Windfisch/analog-synth/measure_vco/experiments/20190922/blue_5.0.png

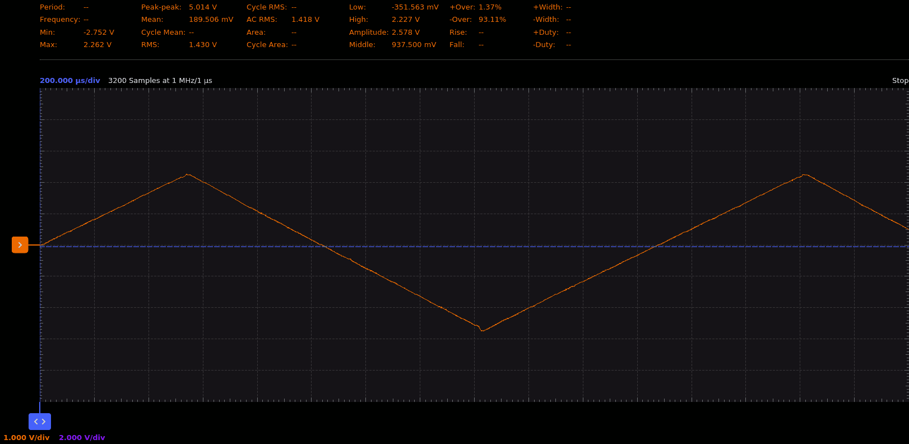
measure_vco/experiments/20190922/blue_5.0.png
