Windfisch/analog-synth/measure_vco/experiments/20190922/breadboard1_8.0.png

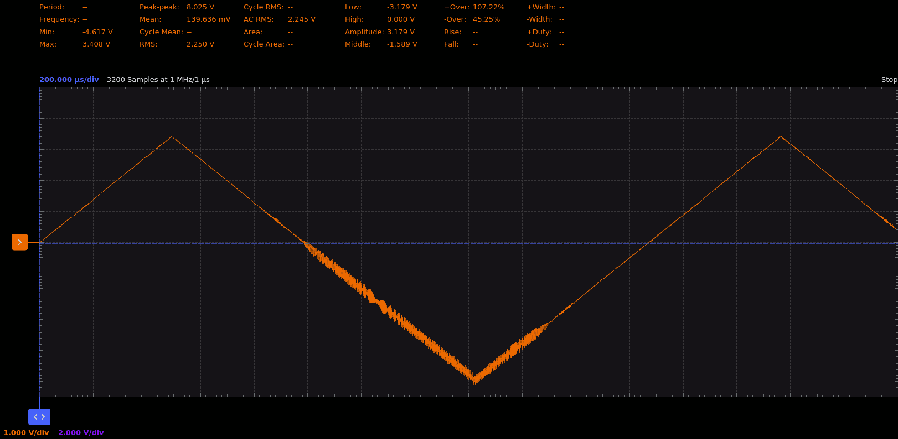
measure_vco/experiments/20190922/breadboard1_8.0.png
