Windfisch/analog-synth/measure_vco/experiments/20190922/breadboard3_2.5.png

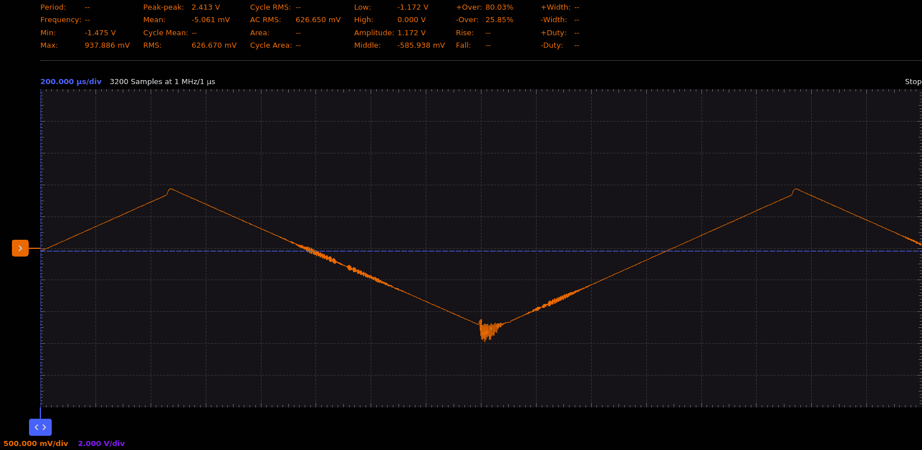
measure_vco/experiments/20190922/breadboard3_2.5.png
