Windfisch/analog-synth/measure_vco/experiments/20190922/breadboard4_2.5.png

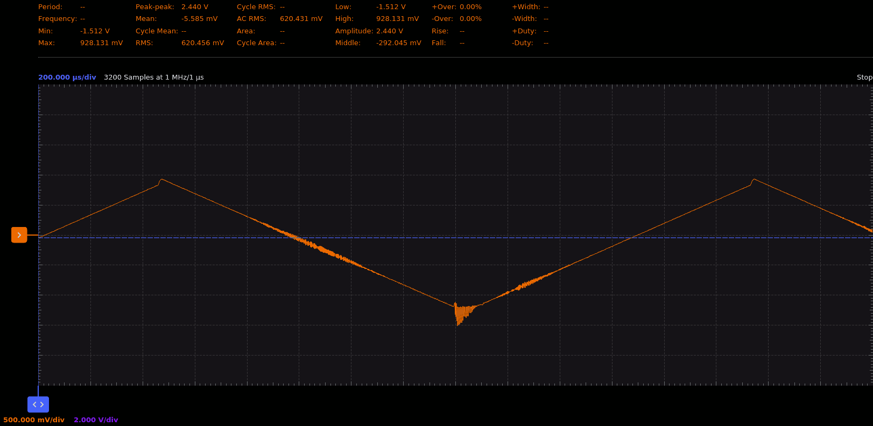
measure_vco/experiments/20190922/breadboard4_2.5.png
