Windfisch/analog-synth/simulation/vca2/vca.kicad_pcb

## KiCad design kicad/HybridIc1.kicad_sch

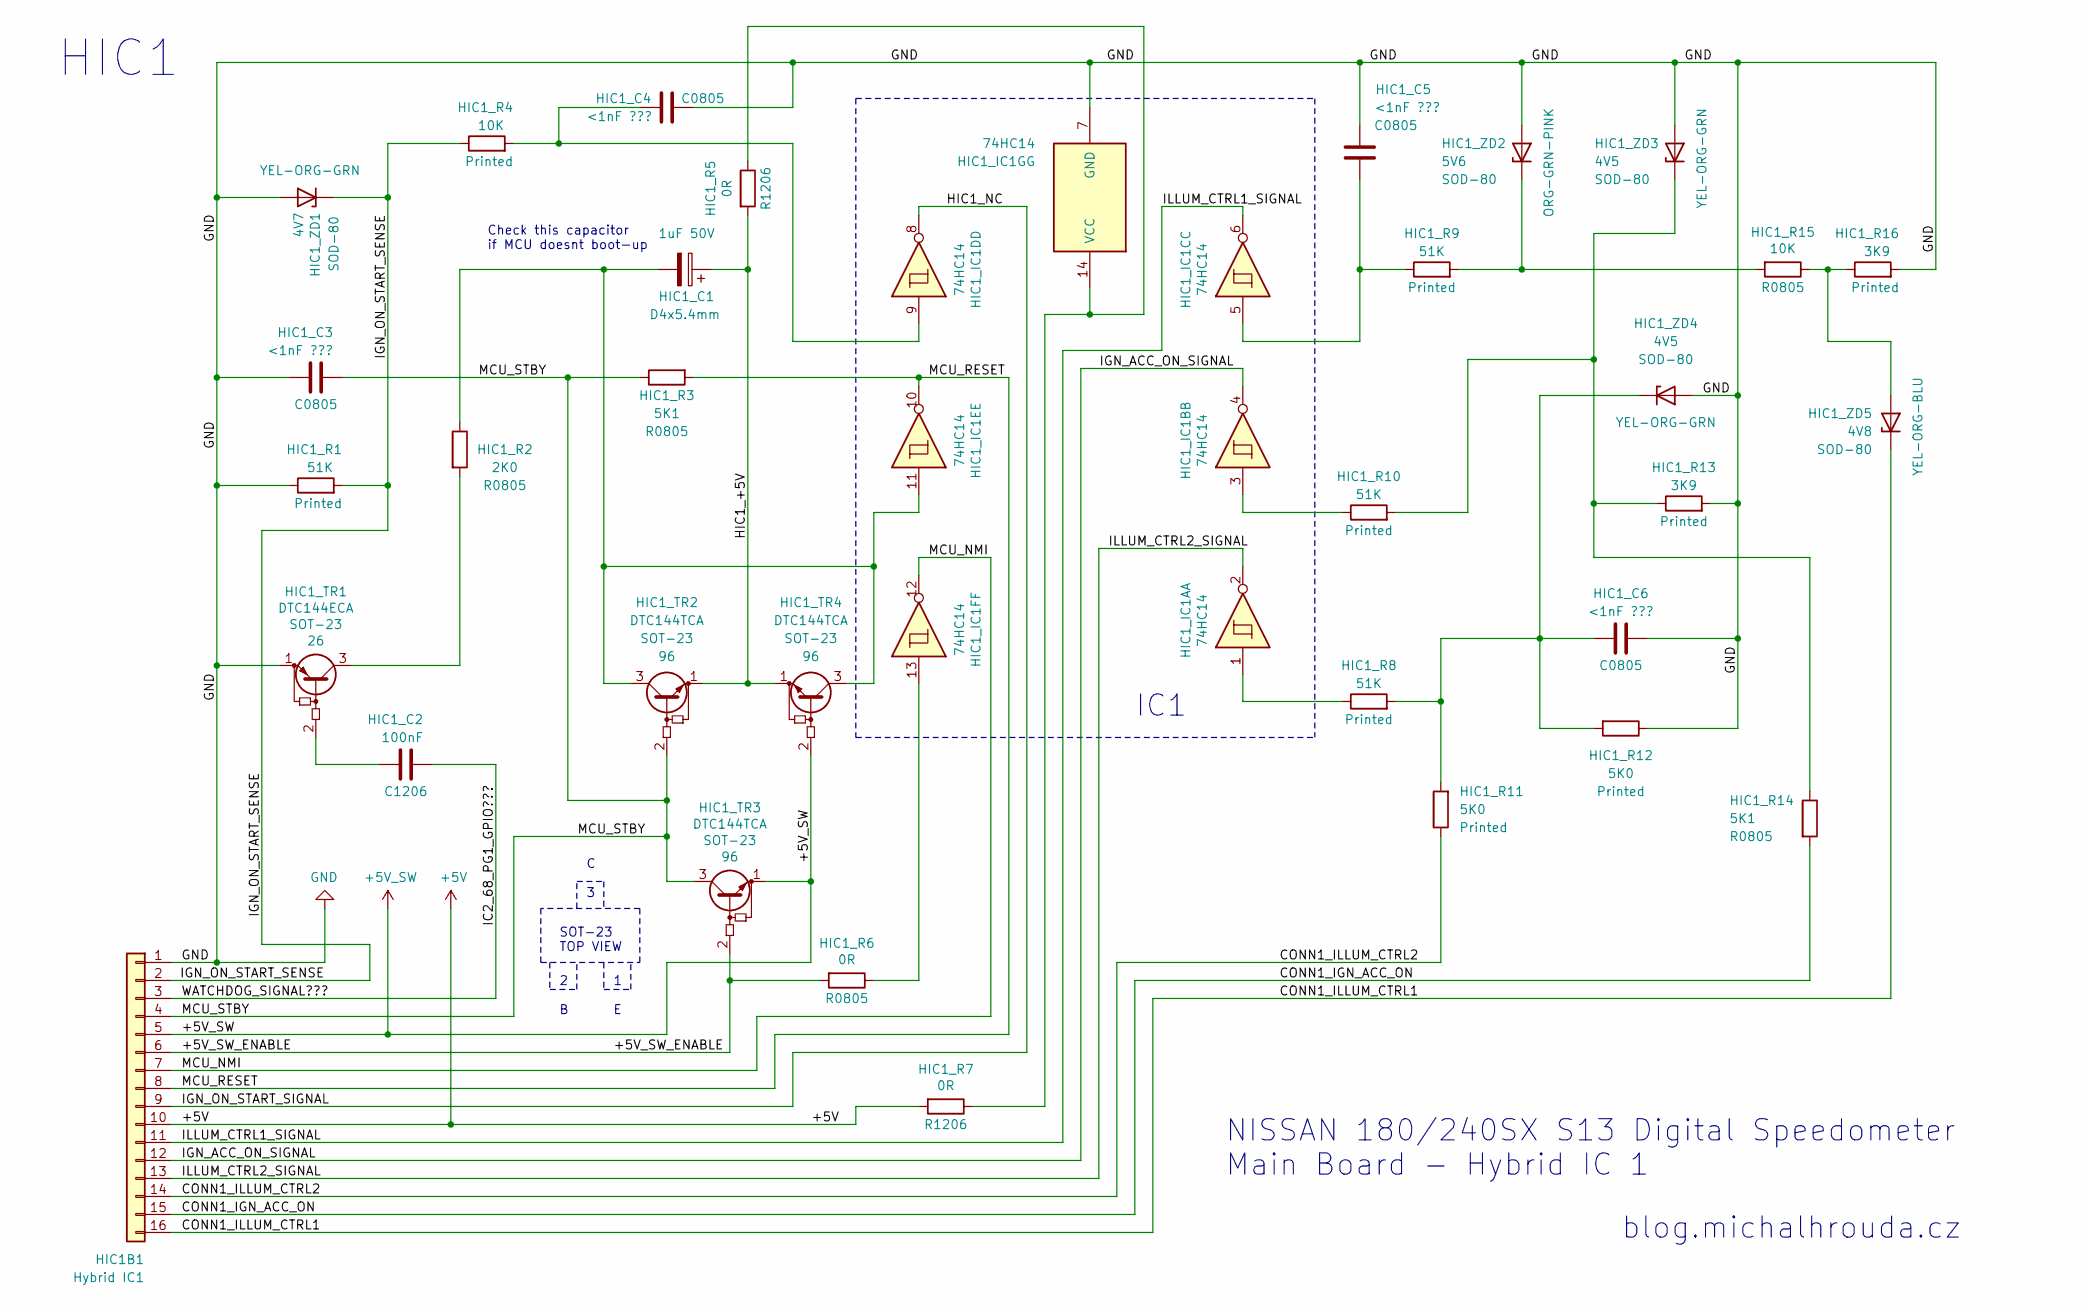
[picture p21: schematic HybridIc1.kicad_sch]

Parts:
HIC1B1: Hybrid IC1
HIC1_C1: 1uF 50V
HIC1_C2: 100nF
HIC1_C3, HIC1_C4, HIC1_C5, HIC1_C6: <1nF ???
HIC1_IC1A, HIC1_IC1B, HIC1_IC1C, HIC1_IC1D, HIC1_IC1E, HIC1_IC1F, HIC1_IC1G: 74HC14
HIC1_R1, HIC1_R8, HIC1_R9, HIC1_R10: 51K
HIC1_R2: 2K0
HIC1_R3, HIC1_R14: 5K1
HIC1_R4, HIC1_R15: 10K
HIC1_R5, HIC1_R6, HIC1_R7: 0R
HIC1_R11, HIC1_R12: 5K0
HIC1_R13, HIC1_R16: 3K9
HIC1_TR1: DTC144ECA
HIC1_TR2, HIC1_TR3, HIC1_TR4: DTC144TCA
HIC1_ZD1: 4V7
HIC1_ZD2: 5V6
HIC1_ZD3, HIC1_ZD4: 4V5
HIC1_ZD5: 4V8

Connections:
+5V: HIC1B1.10, HIC1_R7.2
+5V_SW: HIC1B1.5, HIC1_TR3.1 (E), HIC1_TR4.2 (B)
+5V_SW_ENABLE: HIC1B1.6, HIC1_R6.2, HIC1_TR3.2 (B)
CONN1_IGN_ACC_ON: HIC1B1.15, HIC1_R14.2
CONN1_ILLUM_CTRL1: HIC1B1.16, HIC1_ZD5.1 (K)
CONN1_ILLUM_CTRL2: HIC1B1.14, HIC1_R11.1
GND: HIC1B1.1, HIC1_C3.2, HIC1_C4.2, HIC1_C5.1, HIC1_C6.1, HIC1_IC1G.7 (GND), HIC1_R1.1, HIC1_R12.1, HIC1_R13.2, HIC1_R16.2, HIC1_TR1.1 (E), HIC1_ZD1.2 (A), HIC1_ZD2.2 (A), HIC1_ZD3.2 (A), HIC1_ZD4.2 (A)
HIC1_+5V: HIC1_C1.1, HIC1_R5.2, HIC1_TR2.1 (E), HIC1_TR4.1 (E)
HIC1_NC: HIC1B1.9, HIC1_IC1D.8
IC2_68_PG1_GPIO???: HIC1B1.3, HIC1_C2.1
IGN_ACC_ON_SIGNAL: HIC1B1.12, HIC1_IC1B.4
IGN_ON_START_SENSE: HIC1B1.2, HIC1_R1.2, HIC1_R4.1, HIC1_ZD1.1 (K)
ILLUM_CTRL1_SIGNAL: HIC1B1.11, HIC1_IC1C.6
ILLUM_CTRL2_SIGNAL: HIC1B1.13, HIC1_IC1A.2
MCU_NMI: HIC1B1.7, HIC1_IC1F.12
MCU_RESET: HIC1B1.8, HIC1_IC1E.10, HIC1_R3.2
MCU_STBY: HIC1B1.4, HIC1_C3.1, HIC1_R3.1, HIC1_TR2.2 (B), HIC1_TR3.3 (C)
unnamed: HIC1_C1.2, HIC1_IC1E.11, HIC1_R2.1, HIC1_TR2.3 (C), HIC1_TR4.3 (C)
unnamed: HIC1_C2.2, HIC1_TR1.2 (B)
unnamed: HIC1_C4.1, HIC1_IC1D.9, HIC1_R4.2
unnamed: HIC1_C5.2, HIC1_IC1C.5, HIC1_R9.1
unnamed: HIC1_C6.2, HIC1_R8.2, HIC1_R11.2, HIC1_R12.2, HIC1_ZD4.1 (K)
unnamed: HIC1_IC1A.1, HIC1_R8.1
unnamed: HIC1_IC1B.3, HIC1_R10.1
unnamed: HIC1_IC1F.13, HIC1_R6.1
unnamed: HIC1_IC1G.14 (VCC), HIC1_R5.1, HIC1_R7.1
unnamed: HIC1_R2.2, HIC1_TR1.3 (C)
unnamed: HIC1_R10.2, HIC1_R13.1, HIC1_R14.1, HIC1_ZD3.1 (K)
unnamed: HIC1_R15.1, HIC1_R16.1, HIC1_ZD5.2 (A)
unnamed: HIC1_R9.2, HIC1_R15.2, HIC1_ZD2.1 (K)

Notes on the sheet:
HIC1
NISSAN 180/240SX S13 Digital Speedometer Main Board - Hybrid IC 1
2 B
SOT-23 TOP VIEW
C 3
Check this capacitor if MCU doesnt boot-up
1 E
IC1
blog.michalhrouda.cz
