Windfisch/analog-synth/simulation/vca2/vca.kicad_pcb

## KiCad design kicad/HybridIc3.kicad_sch

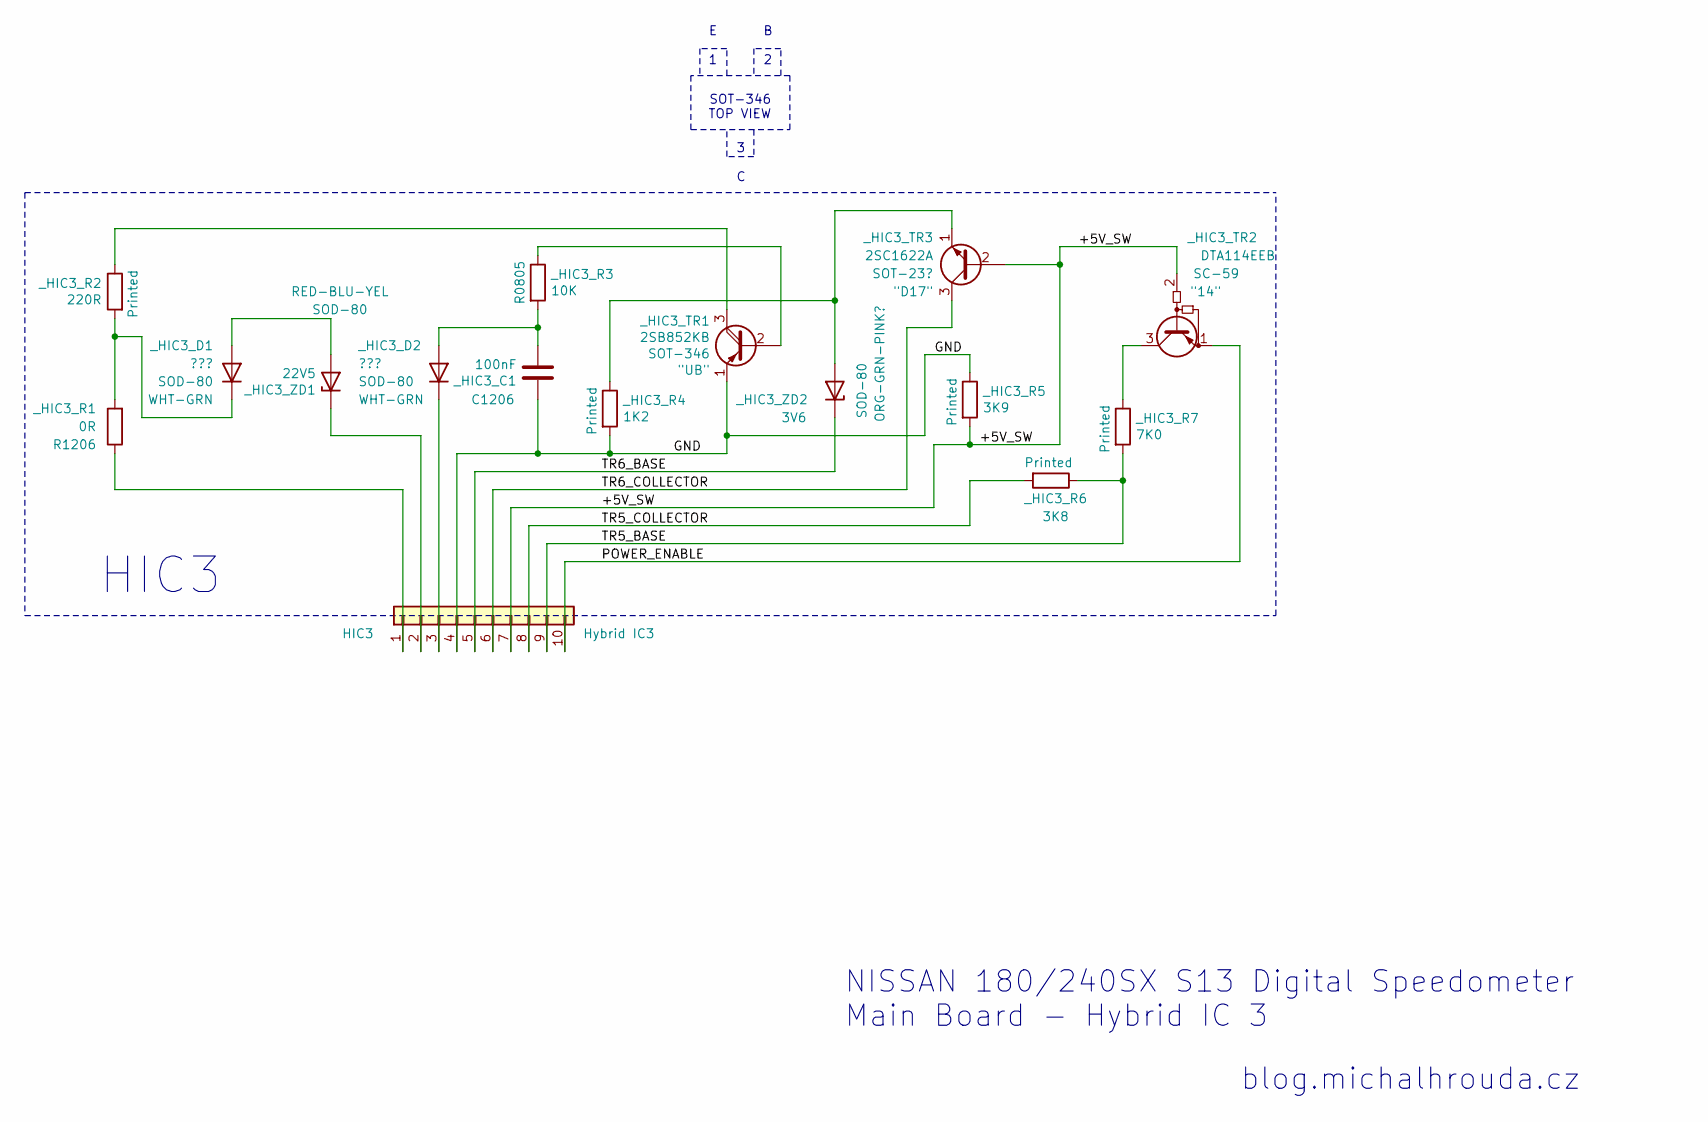
[picture p23: schematic HybridIc3.kicad_sch]

Parts:
HIC3: Hybrid IC3
_HIC3_C1: 100nF
_HIC3_D1, _HIC3_D2: ???
_HIC3_R1: 0R
_HIC3_R2: 220R
_HIC3_R3: 10K
_HIC3_R4: 1K2
_HIC3_R5: 3K9
_HIC3_R6: 3K8
_HIC3_R7: 7K0
_HIC3_TR1: 2SB852KB
_HIC3_TR2: DTA114EEB
_HIC3_TR3: 2SC1622A
_HIC3_ZD1: 22V5
_HIC3_ZD2: 3V6

Connections:
+5V_SW: HIC3.7, _HIC3_R5.2, _HIC3_TR2.2 (B), _HIC3_TR3.2 (B)
GND: HIC3.4, _HIC3_C1.1, _HIC3_R4.2, _HIC3_R5.1, _HIC3_TR1.1 (E)
unnamed: HIC3.1, _HIC3_R1.1
unnamed: HIC3.2, _HIC3_ZD1.1 (K)
unnamed: HIC3.3, _HIC3_D2.1 (K)
unnamed: _HIC3_C1.2, _HIC3_D2.2 (A), _HIC3_R3.2
unnamed: _HIC3_D1.1 (K), _HIC3_R1.2, _HIC3_R2.2
unnamed: _HIC3_D1.2 (A), _HIC3_ZD1.2 (A)
unnamed: _HIC3_R2.1, _HIC3_TR1.3 (C)
unnamed: _HIC3_R3.1, _HIC3_TR1.2 (B)
unnamed: _HIC3_R4.1, _HIC3_TR3.1 (E), _HIC3_ZD2.2 (A)
unnamed: _HIC3_R7.1, _HIC3_TR2.3 (C)
POWER_ENABLE: HIC3.10, _HIC3_TR2.1 (E)
TR5_BASE: HIC3.9, _HIC3_R6.1, _HIC3_R7.2
TR5_COLLECTOR: HIC3.8, _HIC3_R6.2
TR6_BASE: HIC3.5, _HIC3_ZD2.1 (K)
TR6_COLLECTOR: HIC3.6, _HIC3_TR3.3 (C)

Notes on the sheet:
3 C
NISSAN 180/240SX S13 Digital Speedometer Main Board - Hybrid IC 3
E 1
blog.michalhrouda.cz
HIC3
SOT-346 TOP VIEW
B 2
