Windfisch/analog-synth/simulation/vca2/vca.kicad_pcb

## KiCad design kicad/MainBoard.kicad_sch

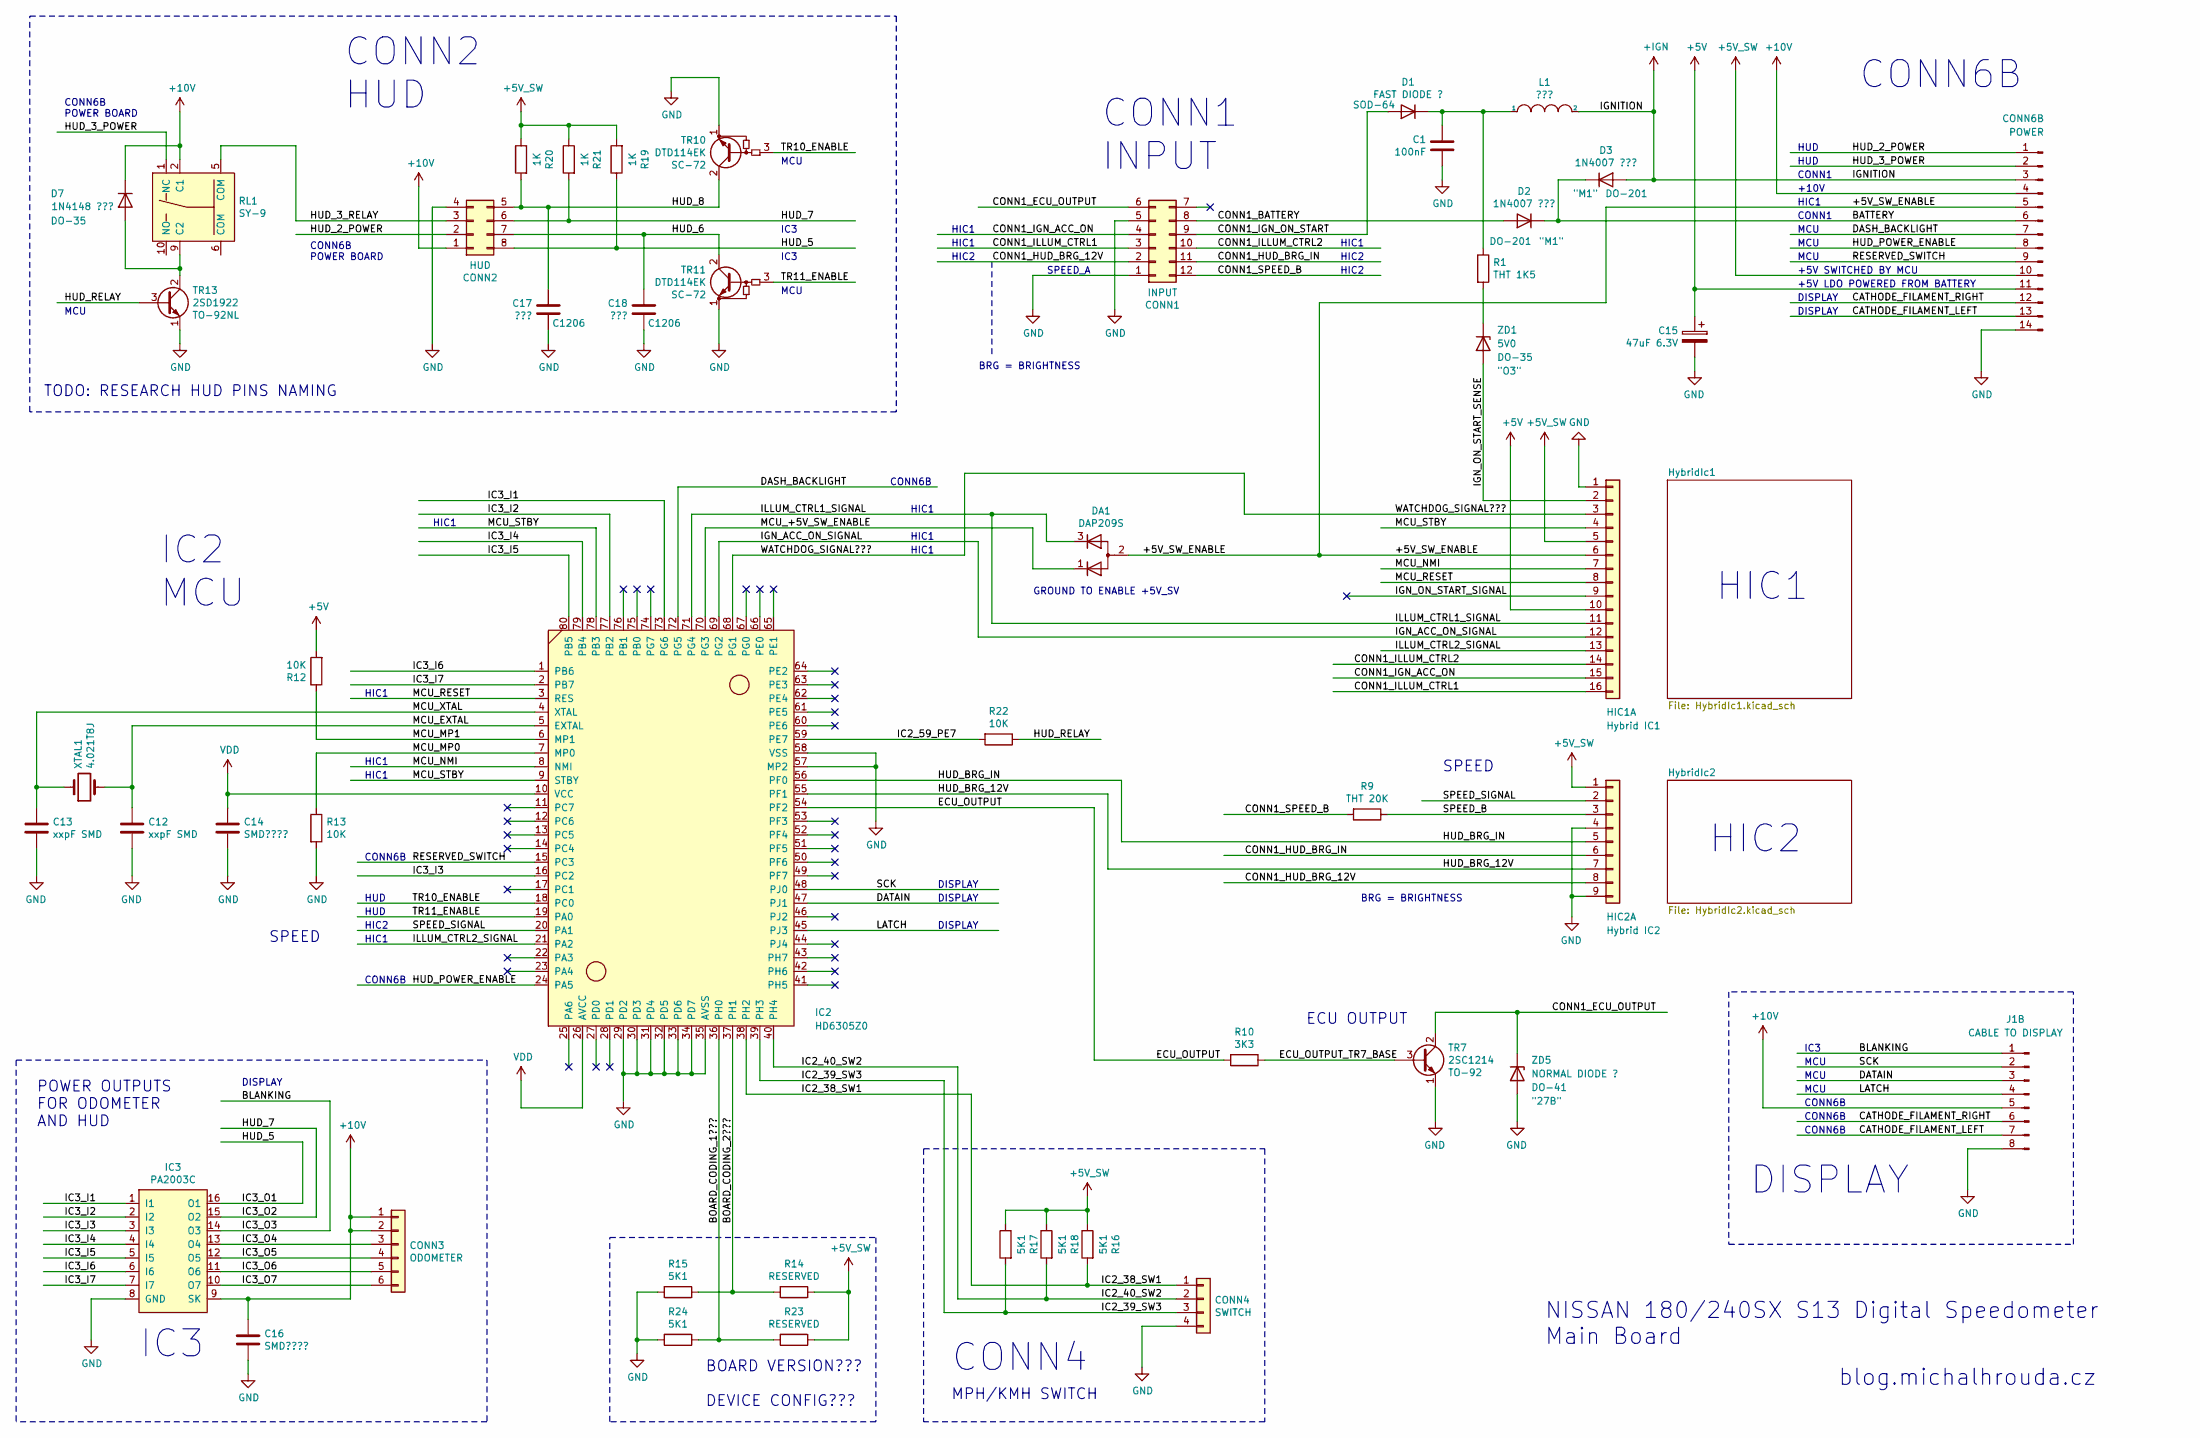
[picture p24: schematic MainBoard.kicad_sch]

Parts:
C1: 100nF
C12, C13: xxpF SMD
C14, C16: SMD????
C15: 47uF 6.3V
C17, C18: ???
CONN1: INPUT
CONN2: HUD
CONN3: ODOMETER
CONN4: SWITCH
CONN6B: POWER
D1: FAST DIODE ?
D2, D3: 1N4007 ???
D7: 1N4148 ???
DA1: DAP209S
HIC1A: Hybrid IC1
HIC2A: Hybrid IC2
IC2: HD6305Z0
IC3: PA2003C
J1B: CABLE TO DISPLAY
L1: ???
R1: THT 1K5
R9: THT 20K
R10: 3K3
R12, R13, R22: 10K
R14, R23: RESERVED
R15, R16, R17, R18, R24: 5K1
R19, R20, R21: 1K
RL1: SY-9
TR7: 2SC1214
TR10, TR11: DTD114EK
TR13: 2SD1922
XTAL1: 4.021T8J
ZD1: 5V0
ZD5: NORMAL DIODE ?

Connections:
+5V: C15.1, CONN6B.11, HIC1A.10, R12.2
+5V_SW: CONN6B.10, HIC1A.5, HIC2A.1, R14.1, R16.1, R17.1, R18.1, R19.2, R20.1, R21.1, R23.1
+5V_SW_ENABLE: CONN6B.5, DA1.2 (A), HIC1A.6
+10V: C16.1, CONN2.1, CONN3.1, CONN3.2, CONN6B.4, D7.1 (K), IC3.9 (SK), J1B.5, RL1.2 (C1)
+IGN: CONN6B.3, D3.2 (A), L1.2
BATTERY: CONN6B.6, D2.1 (K), D3.1 (K)
BLANKING: IC3.14 (O3), J1B.1
BOARD_CODING_1???: IC2.36 (PH0), R23.2, R24.1
BOARD_CODING_2???: IC2.37 (PH1), R14.2, R15.1
CATHODE_FILAMENT_LEFT: CONN6B.13, J1B.7
CATHODE_FILAMENT_RIGHT: CONN6B.12, J1B.6
CONN1_BATTERY: CONN1.8, D2.2 (A)
CONN1_ECU_OUTPUT: CONN1.6, TR7.2 (C), ZD5.1 (K)
CONN1_HUD_BRG_12V: CONN1.2, HIC2A.8
CONN1_HUD_BRG_IN: CONN1.11, HIC2A.6
CONN1_IGN_ACC_ON: CONN1.4, HIC1A.15
CONN1_IGN_ON_START: CONN1.9, D1.2 (A)
CONN1_ILLUM_CTRL1: CONN1.3, HIC1A.16
CONN1_ILLUM_CTRL2: CONN1.10, HIC1A.14
CONN1_SPEED_B: CONN1.12, R9.2
DASH_BACKLIGHT: CONN6B.7, IC2.72 (PG5)
DATAIN: IC2.47 (PJ1), J1B.3
ECU_OUTPUT: IC2.54 (PF2), R10.2
ECU_OUTPUT_TR7_BASE: R10.1, TR7.3 (B)
GND: C1.2, C12.2, C13.2, C14.2, C15.2, C16.2, C17.2, C18.2, CONN1.1, CONN1.5, CONN2.4, CONN4.4, CONN6B.14, HIC1A.1, HIC2A.4, HIC2A.9, IC2.29 (PD2), IC2.30 (PD3), IC2.31 (PD4), IC2.32 (PD5), IC2.33 (PD6), IC2.34 (PD7), IC2.35 (AVSS), IC2.57 (MP2), IC2.58 (VSS), IC3.8 (GND), J1B.8, R13.2, R15.2, R24.2, TR7.1 (E), TR10.1 (E), TR11.1 (E), TR13.1 (E), ZD5.2 (A)
HUD_2_POWER: CONN2.2, CONN6B.1
HUD_3_POWER: CONN6B.2, RL1.1 (NC)
HUD_3_RELAY: CONN2.3, RL1.5 (COM)
HUD_5: CONN2.8, IC3.16 (O1), R19.1
HUD_6: C18.1, CONN2.7, TR11.2 (C)
HUD_7: CONN2.6, IC3.15 (O2), R21.2
HUD_8: C17.1, CONN2.5, R20.2, TR10.2 (C)
HUD_BRG_12V: HIC2A.7, IC2.55 (PF1)
HUD_BRG_IN: HIC2A.5, IC2.56 (PF0)
HUD_POWER_ENABLE: CONN6B.8, IC2.24 (PA5)
HUD_RELAY: R22.1, TR13.3 (B)
IC2_38_SW1: CONN4.1, IC2.38 (PH2), R16.2
IC2_39_SW3: CONN4.3, IC2.39 (PH3), R17.2
IC2_40_SW2: CONN4.2, IC2.40 (PH4), R18.2
IC2_59_PE7: IC2.59 (PE7), R22.2
IC3_I1: IC2.73 (PG6), IC3.1 (I1)
IC3_I2: IC2.77 (PB2), IC3.2 (I2)
IC3_I3: IC2.16 (PC2), IC3.3 (I3)
IC3_I4: IC2.79 (PB4), IC3.4 (I4)
IC3_I5: IC2.80 (PB5), IC3.5 (I5)
IC3_I6: IC2.1 (PB6), IC3.6 (I6)
IC3_I7: IC2.2 (PB7), IC3.7 (I7)
IC3_O4: CONN3.3, IC3.13 (O4)
IC3_O5: CONN3.4, IC3.12 (O5)
IC3_O6: CONN3.5, IC3.11 (O6)
IC3_O7: CONN3.6, IC3.10 (O7)
IGN_ACC_ON_SIGNAL: HIC1A.12, IC2.69 (PG2)
IGN_ON_START_SENSE: HIC1A.2, ZD1.2 (A)
IGN_ON_START_SIGNAL: HIC1A.9
ILLUM_CTRL1_SIGNAL: DA1.3 (K), HIC1A.11, IC2.71 (PG4)
ILLUM_CTRL2_SIGNAL: HIC1A.13, IC2.21 (PA2)
LATCH: IC2.45 (PJ3), J1B.4
MCU_+5V_SW_ENABLE: DA1.1 (K), IC2.70 (PG3)
MCU_EXTAL: C12.1, IC2.5 (EXTAL), XTAL1.2
MCU_MP0: IC2.7 (MP0), R13.1
MCU_MP1: IC2.6 (MP1), R12.1
MCU_NMI: HIC1A.7, IC2.8 (NMI)
MCU_RESET: HIC1A.8, IC2.3 (RES)
MCU_STBY: HIC1A.4, IC2.9 (STBY), IC2.78 (PB3)
MCU_XTAL: C13.1, IC2.4 (XTAL), XTAL1.1
unnamed: C1.1, D1.1 (K), L1.1, R1.1
unnamed: D7.2 (A), RL1.9 (C2), TR13.2 (C)
unnamed: R1.2, ZD1.1 (K)
RESERVED_SWITCH: CONN6B.9, IC2.15 (PC3)
SCK: IC2.48 (PJ0), J1B.2
SPEED_B: HIC2A.3, R9.1
SPEED_SIGNAL: HIC2A.2, IC2.20 (PA1)
TR10_ENABLE: IC2.18 (PC0), TR10.3 (B)
TR11_ENABLE: IC2.19 (PA0), TR11.3 (B)
VDD: C14.1, IC2.10 (VCC), IC2.26 (AVCC)
WATCHDOG_SIGNAL???: HIC1A.3, IC2.68 (PG1)

Notes on the sheet:
MCU
blog.michalhrouda.cz
HIC1
CONN6B
IC3
TODO: RESEARCH HUD PINS NAMING
+10V
BRG = BRIGHTNESS
HIC2
CONN6B POWER BOARD
HUD
BOARD VERSION??? DEVICE CONFIG???
DISPLAY
ECU OUTPUT
+5V SWITCHED BY MCU
SPEED
MPH/KMH SWITCH
NISSAN 180/240SX S13 Digital Speedometer Main Board
CONN4
SPEED_A
CONN1
CONN2 HUD
CONN1 INPUT
+5V LDO POWERED FROM BATTERY
POWER OUTPUTS FOR ODOMETER AND HUD
IC2 MCU
GROUND TO ENABLE +5V_SV
