Windfisch/analog-synth/simulation/vca2/vca.kicad_pcb

## KiCad design kicad/PowerBoard.kicad_sch

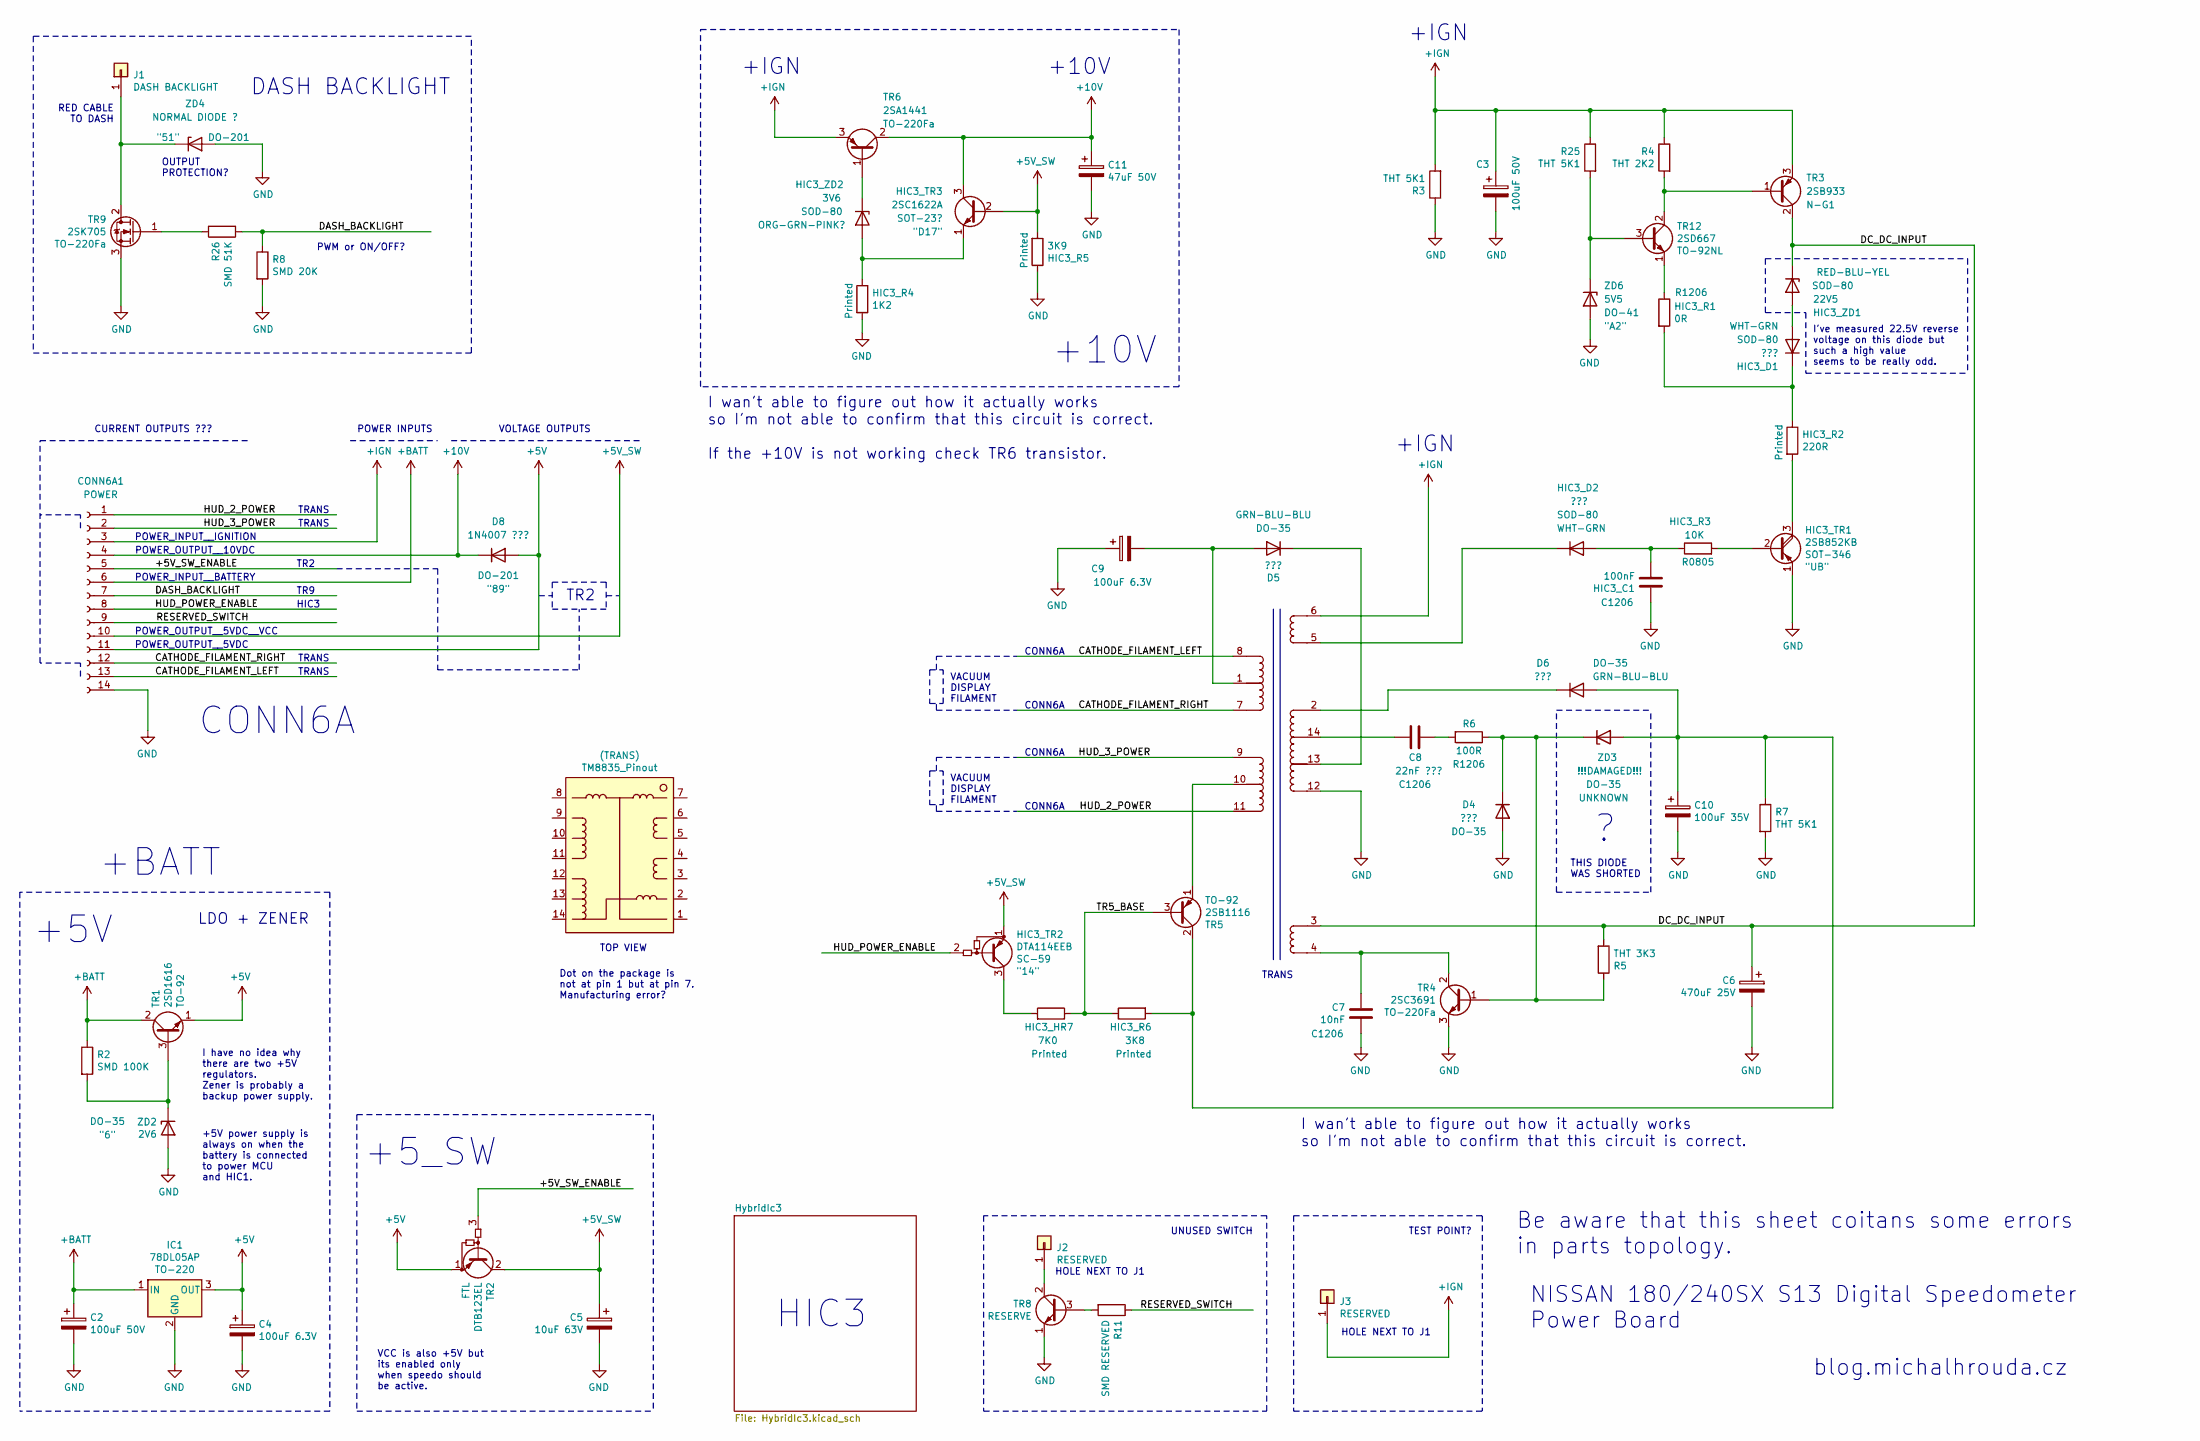
[picture p25: schematic PowerBoard.kicad_sch]

Parts:
(TRANS): TM8835_Pinout
C2, C3: 100uF 50V
C4, C9: 100uF 6.3V
C5: 10uF 63V
C6: 470uF 25V
C7: 10nF
C8: 22nF ???
C10: 100uF 35V
C11: 47uF 50V
CONN6A1: POWER
D4, D5, D6: ???
D8: 1N4007 ???
HIC3_C1: 100nF
HIC3_D1, HIC3_D2: ???
HIC3_HR7: 7K0
HIC3_R1: 0R
HIC3_R2: 220R
HIC3_R3: 10K
HIC3_R4: 1K2
HIC3_R5: 3K9
HIC3_R6: 3K8
HIC3_TR1: 2SB852KB
HIC3_TR2: DTA114EEB
HIC3_TR3: 2SC1622A
HIC3_ZD1: 22V5
HIC3_ZD2: 3V6
IC1: 78DL05AP
J1: DASH BACKLIGHT
J2, J3: RESERVED
R2: SMD 100K
R3, R7, R25: THT 5K1
R4: THT 2K2
R5: THT 3K3
R6: 100R
R8: SMD 20K
R11: SMD RESERVED
R26: SMD 51K
TR1: 2SD1616
TR2: DTB123EL
TR3: 2SB933
TR4: 2SC3691
TR5: 2SB1116
TR6: 2SA1441
TR8: RESERVE
TR9: 2SK705
TR12: 2SD667
TRANS1A, TRANS1B, TRANS1C, TRANS1D, TRANS1E: TM8835
ZD2: 2V6
ZD3: !!!DAMAGED!!!
ZD4: NORMAL DIODE ?
ZD6: 5V5

Connections:
+5V: C4.1, CONN6A1.11, D8.2 (A), IC1.3 (OUT), TR1.1 (E), TR2.1 (E)
+5V_SW: C5.1, CONN6A1.10, HIC3_TR2.1 (E), TR2.2 (C)
+5V_SW_ENABLE: CONN6A1.5, TR2.3 (B)
+10V: C11.1, CONN6A1.4, D8.1 (K), HIC3_TR3.3 (C), TR6.2 (C)
+BATT: C2.1, CONN6A1.6, IC1.1 (IN), R2.1, TR1.2 (C)
+IGN: C3.1, CONN6A1.3, J3.1, R3.2, R4.1, R25.1, TR3.3 (E), TR6.3 (E), TRANS1C.6
CATHODE_FILAMENT_LEFT: CONN6A1.13, TRANS1A.8
CATHODE_FILAMENT_RIGHT: CONN6A1.12, TRANS1A.7
DASH_BACKLIGHT: CONN6A1.7, R8.1, R26.2
DC_DC_INPUT: C6.1, HIC3_ZD1.1 (K), R5.2, TR3.2 (C), TRANS1B.3
GND: C2.2, C3.2, C4.2, C5.2, C6.2, C7.2, C9.1, C10.2, C11.2, CONN6A1.14, D4.2 (A), IC1.2 (GND), R3.1, R7.2, R8.2, TR4.3 (E), TR8.1 (E), TR9.3 (S), TRANS1E.12, ZD2.2 (A), ZD4.2 (A), ZD6.2 (A)
HUD_2_POWER: CONN6A1.1, TRANS1D.11
HUD_3_POWER: CONN6A1.2, TRANS1D.9
HUD_POWER_ENABLE: CONN6A1.8, HIC3_TR2.2 (B)
unnamed: C7.1, TR4.2 (C), TRANS1B.4
unnamed: C8.1, R6.2
unnamed: C8.2, TRANS1E.14
unnamed: C9.2, D5.2 (A), TRANS1A.1
unnamed: C10.1, D6.2 (A), HIC3_R6.2, R7.1, TR5.2 (C), ZD3.2 (A)
unnamed: D4.1 (K), R5.1, R6.1, TR4.1 (B), ZD3.1 (K)
unnamed: D5.1 (K), TRANS1E.13
unnamed: D6.1 (K), TRANS1E.2
unnamed: HIC3_C1.2, HIC3_D2.2 (A), HIC3_R3.1
unnamed: HIC3_D1.1 (K), HIC3_R1.2, HIC3_R2.1
unnamed: HIC3_D1.2 (A), HIC3_ZD1.2 (A)
unnamed: HIC3_D2.1 (K), TRANS1C.5
unnamed: HIC3_HR7.2, HIC3_TR2.3 (C)
unnamed: HIC3_R1.1, TR12.1 (E)
unnamed: HIC3_R2.2, HIC3_TR1.3 (C)
unnamed: HIC3_R3.2, HIC3_TR1.2 (B)
unnamed: HIC3_R4.1, HIC3_TR3.1 (E), HIC3_ZD2.2 (A)
unnamed: HIC3_R5.2, HIC3_TR3.2 (B)
unnamed: HIC3_ZD2.1 (K), TR6.1 (B)
unnamed: J1.1, TR9.2 (D), ZD4.1 (K)
unnamed: J2.1, TR8.2 (C)
unnamed: R2.2, TR1.3 (B), ZD2.1 (K)
unnamed: R4.2, TR3.1 (B), TR12.2 (C)
unnamed: R11.2, TR8.3 (B)
unnamed: R25.2, TR12.3 (B), ZD6.1 (K)
unnamed: R26.1, TR9.1 (G)
unnamed: TR5.1 (E), TRANS1D.10
RESERVED_SWITCH: CONN6A1.9, R11.1
TR5_BASE: HIC3_HR7.1, HIC3_R6.1, TR5.3 (B)

Notes on the sheet:
CONN6A
+10V
I've measured 22.5V reverse voltage on this diode but such a high value seems to be really odd.
Dot on the package is not at pin 1 but at pin 7. Manufacturing error?
VACUUM DISPLAY FILAMENT
+5V
HOLE NEXT TO J1
+5_SW
POWER_OUTPUT__5VDC__VCC
TRANS
UNUSED SWITCH
TEST POINT?
OUTPUT PROTECTION?
POWER INPUTS
I wan't able to figure out how it actually works so I'm not able to confirm that this circuit is correct.
POWER_OUTPUT__5VDC
blog.michalhrouda.cz
I have no idea why there are two +5V regulators. Zener is probably a backup power supply.
+IGN
POWER_INPUT__BATTERY
HIC3
VCC is also +5V but its enabled only when speedo should be active.
TR9
VOLTAGE OUTPUTS
TR2
PWM or ON/OFF?
POWER_INPUT__IGNITION
DASH BACKLIGHT
LDO + ZENER
+BATT
POWER_OUTPUT__10VDC
TOP VIEW
NISSAN 180/240SX S13 Digital Speedometer Power Board
I wan't able to figure out how it actually works so I'm not able to confirm that this circuit is correct. If the +10V is not working check TR6 transistor.
THIS DIODE WAS SHORTED
Be aware that this sheet coitans some errors in parts topology.
RED CABLE TO DASH
+5V power supply is always on when the battery is connected to power MCU and HIC1.
CURRENT OUTPUTS ???
