Windfisch/analog-synth/measure_vco/schem/measure_vco.sch

## KiCad design measure_vco/schem/measure_vco.sch (2019-10-25)

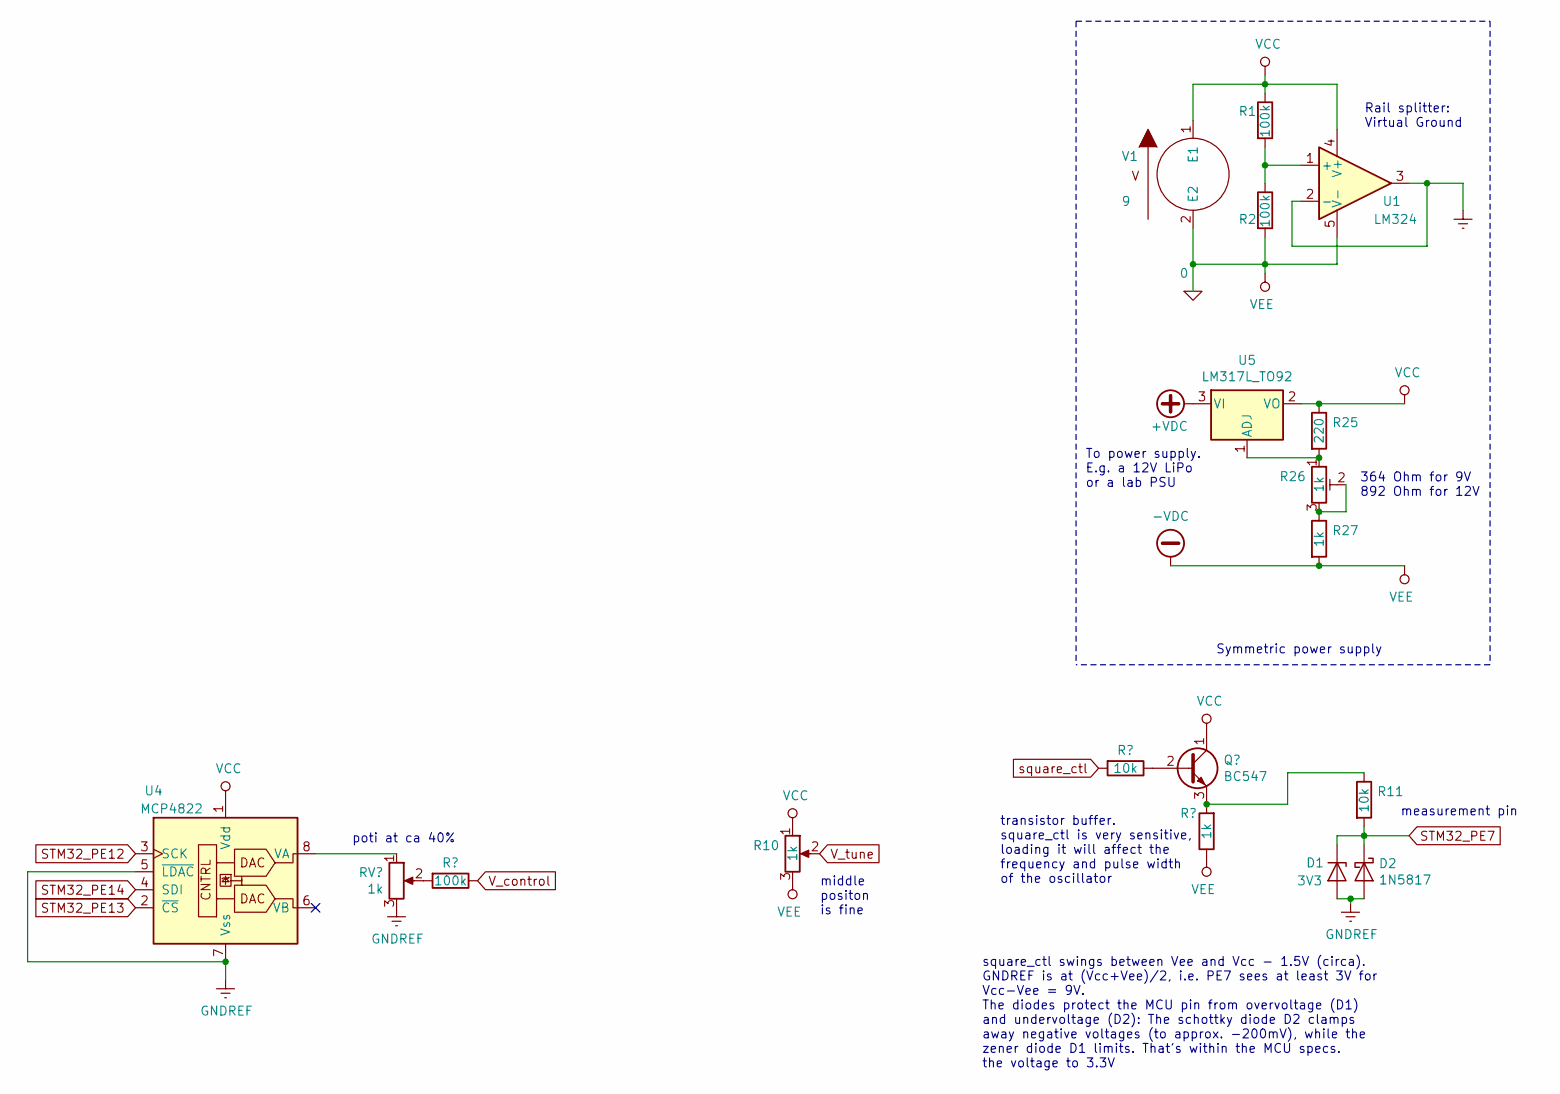
[picture p26: schematic measure_vco.sch]

Parts:
D1: 3V3
D2: 1N5817; D_DO-41_SOD81_P10.16mm_Horizontal
R1, R2: 100k
R10, R26, R27: 1k
R11: 10k
R25: 220
U1: LM324
U4: MCP4822
U5: LM317L_TO92; TO-92_Inline
V1: 9

Connections:
+VDC: U5.3 (VI)
-VDC: R2.2, R10.3, R27.2, U1.5 (V-), V1.2 (E2)
GNDREF: D1.2 (A), D2.2 (A), U1.2 (-), U1.3, U4.5 (~LDAC), U4.7 (Vss)
unnamed: R1.2, R2.1, U1.1 (+)
unnamed: R25.2, R26.1, U5.1 (ADJ)
unnamed: R26.2, R26.3, R27.1
STM32_PE7: D1.1 (K), D2.1 (K), R11.2
STM32_PE12: U4.3 (SCK)
STM32_PE13: U4.2 (~CS)
STM32_PE14: U4.4 (SDI)
VCC: R1.1, R10.1, R25.1, U1.4 (V+), U4.1 (Vdd), U5.2 (VO), V1.1 (E1)
V_tune: R10.2

Notes on the sheet:
middle positon is fine
measurement pin
square_ctl swings between Vee and Vcc - 1.5V (circa). GNDREF is at (Vcc+Vee)/2, i.e. PE7 sees at least 3V for Vcc-Vee = 9V. The diodes protect the MCU pin from overvoltage (D1) and undervoltage (D2): The schottky diode D2 clamps away negative voltages (to approx. -200mV), while the zener diode D1 l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
Rail splitter: Virtual Ground
364 Ohm for 9V 892 Ohm for 12V
To power supply. E.g. a 12V LiPo or a lab PSU
Symmetric power supply
transistor buffer. square_ctl is very sensitive, loading it will affect the frequency and pulse width of the oscillator
poti at ca 40%
